smesh-stanford/smesh/snode/data_before_2024_11_07/network_tests/4004_ina260.csv

2024-11-02 09:39:09.005195 | 0x336918e8 | 13.24 |  | 5.75 | 5 | -64 | 5
2024-11-02 09:40:10.199133 | 0x336918e8 | 13.23625 | -1.25 | 5.75 | 5 | -65 | 5
2024-11-02 09:41:08.960617 | 0x336918e8 | 13.1825 | 1.25 | 6.0 | 5 | -61 | 5
2024-11-02 09:42:10.821677 | 0x336918e8 | 13.24375 |  | 6.0 | 5 | -68 | 5
2024-11-02 09:43:10.251887 | 0x336918e8 | 13.195 |  | 6.5 | 5 | -63 | 5
2024-11-02 09:44:10.046971 | 0x336918e8 | 13.22875 | -1.25 | 6.5 | 5 | -61 | 5
2024-11-02 09:44:55.519510 | 0x336918e8 | 13.23 | -2.5 | 6.5 | 5 | -59 | 5
2024-11-02 09:45:54.516993 | 0x336918e8 | 13.23 | 1.25 | 6.25 | 5 | -59 | 5
2024-11-02 09:46:54.605464 | 0x336918e8 | 13.24375 | -1.25 | 5.75 | 5 | -69 | 5
2024-11-02 09:47:54.824052 | 0x336918e8 | 13.25125 | -1.25 | 6.5 | 5 | -62 | 5
2024-11-02 09:48:55.226775 | 0x336918e8 | 13.18875 |  | 6.25 | 5 | -61 | 5
2024-11-02 09:49:56.953843 | 0x336918e8 | 13.24375 |  | 6.0 | 5 | -61 | 5
2024-11-02 09:50:57.016866 | 0x336918e8 | 13.185 |  | 6.5 | 5 | -61 | 5
2024-11-02 09:51:43.167883 | 0x433abf20 | 13.3075 | 63.75 | 6.25 | 7 | -21 | 7
2024-11-02 09:51:55.764876 | 0x336918e8 | 13.2275 | 1.25 | 6.5 | 5 | -66 | 5
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
