smesh-stanford/smesh/snode/data_before_2024_11_07/network_tests/4004_pmsa003i.csv

2024-11-02 09:39:28.377175 | 0x4358fbec | 48 | 48 | 48 | 36 | 44 | 48 | -2.0 | 6 | -93 | 6
2024-11-02 09:40:27.102049 | 0x4358fbec | 39 | 39 | 39 | 33 | 38 | 39 | 5.75 | 6 | -63 | 6
2024-11-02 09:41:27.211444 | 0x4358fbec | 53 | 53 | 53 | 40 | 46 | 53 | 6.0 | 6 | -67 | 6
2024-11-02 09:42:27.597850 | 0x4358fbec | 44 | 44 | 44 | 35 | 42 | 44 | 6.0 | 6 | -61 | 6
2024-11-02 09:43:30.037312 | 0x4358fbec | 45 | 45 | 45 | 36 | 42 | 45 | 5.75 | 6 | -64 | 6
2024-11-02 09:44:29.834404 | 0x4358fbec | 47 | 47 | 47 | 37 | 43 | 47 | 7.25 | 6 | -65 | 6
2024-11-02 09:44:45.331704 | 0x336918e8 |  |  |  |  |  |  | 6.75 | 5 | -61 | 5
2024-11-02 09:44:53.163546 | 0x433efcb4 |  |  |  |  |  |  | 6.25 | 3 | -61 | 3
2024-11-02 09:45:28.566304 | 0x4358fbec | 43 | 43 | 43 | 35 | 40 | 43 | 7.25 | 6 | -58 | 6
2024-11-02 09:46:30.786763 | 0x4358fbec | 28 | 28 | 28 | 27 | 28 | 28 | 7.0 | 6 | -68 | 6
2024-11-02 09:46:39.595647 | 0x4358db28 |  |  |  |  |  |  | 5.75 | 7 | -35 | 7
2024-11-02 09:47:29.545237 | 0x4358fbec | 44 | 44 | 44 | 37 | 42 | 44 | 6.5 | 6 | -61 | 6
2024-11-02 09:47:46.579088 | 0x4358db28 |  |  |  |  |  |  | 6.5 | 7 | -47 | 7
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
