smesh-stanford/smesh/snode/data_before_2024_11_07/network_tests/{nodeid}_bme688.csv

2024-11-02 09:38:20.419089 | 0x336918e8 | 24.95269 | 40.599884 | 1011.98816 | 141.12459 | 231 | 6.25 | 5 | -61 | 5
2024-11-02 09:38:24.275060 | 0x433efcb4 | 25.771275 | 36.366066 | 1011.4749 | 660.741 | 112 | 6.0 | 3 | -61 | 3
2024-11-02 09:38:28.500848 | 0x4358fbec | 27.368664 | 33.620113 | 1011.6055 | 448.43442 | 89 | 5.75 | 6 | -63 | 6
2024-11-02 09:38:40.127914 | 0x336918e8 | 24.950157 | 40.697857 | 1011.98755 | 141.94621 | 230 | 6.25 | 5 | -62 | 5
2024-11-02 09:38:43.241827 | 0x433efcb4 | 25.77374 | 36.34227 | 1011.48456 | 666.0006 | 109 | 5.75 | 3 | -73 | 3
